sentrihome/Home-Security/ESPFirmwareV2/3d-Print/UART + Display layout_UART + Display layout v8_ESPsocketMount v8_2_Clamp2.stl

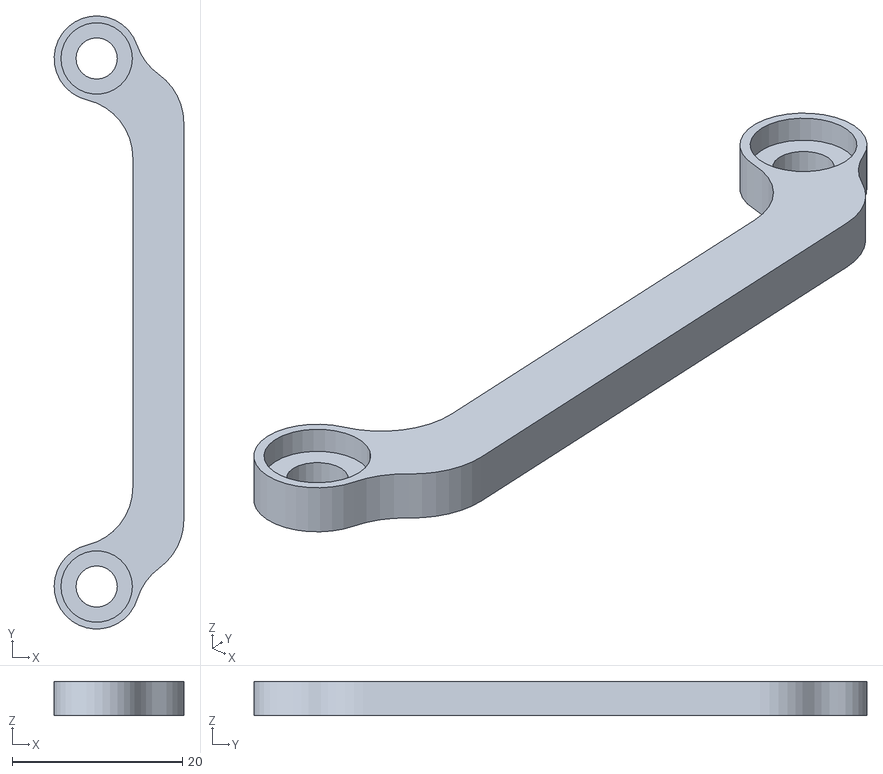
[picture p25: CAD file, 2026-08-16]
ESPFirmwareV2/3d-Print/UART + Display layout_UART + Display layout v8_ESPsocketMount v8_2_Clamp2.stl
15.3 x 72.1 x 4.00
