sentrihome/Home-Security/ESPFirmwareV2/Circuit/Circuit Drawings/HomeSecurity-Circuits-NPTH-drl_map.dxf

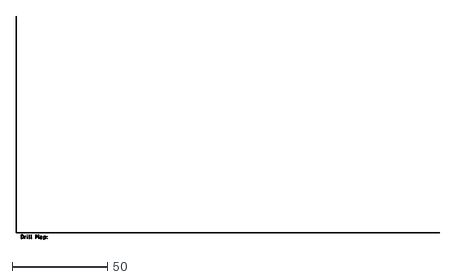
[picture p26: CAD file, 2026-08-16]
ESPFirmwareV2/Circuit/Circuit Drawings/HomeSecurity-Circuits-NPTH-drl_map.dxf
222.0 x 117.2
