sentrihome/Home-Security/ESPFirmwareV2/Circuit/Circuit Drawings/(Unsaved)_(Unsaved)_Body1.stl

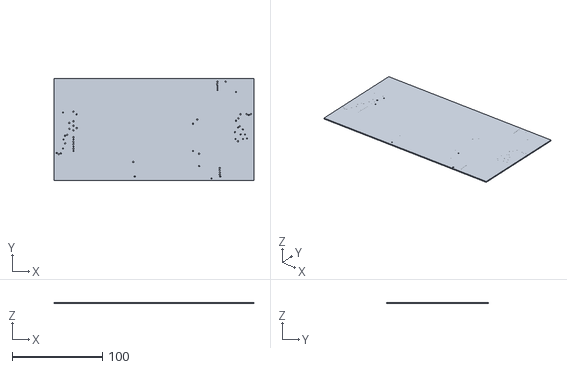
[picture p27: CAD file, 2026-08-16]
ESPFirmwareV2/Circuit/Circuit Drawings/(Unsaved)_(Unsaved)_Body1.stl
222.0 x 113.3 x 1.10
