sentrihome/Home-Security/ESPFirmwareV2/Circuit/Circuit Drawings/HomeSecurity-Circuits-B_Cu.dxf

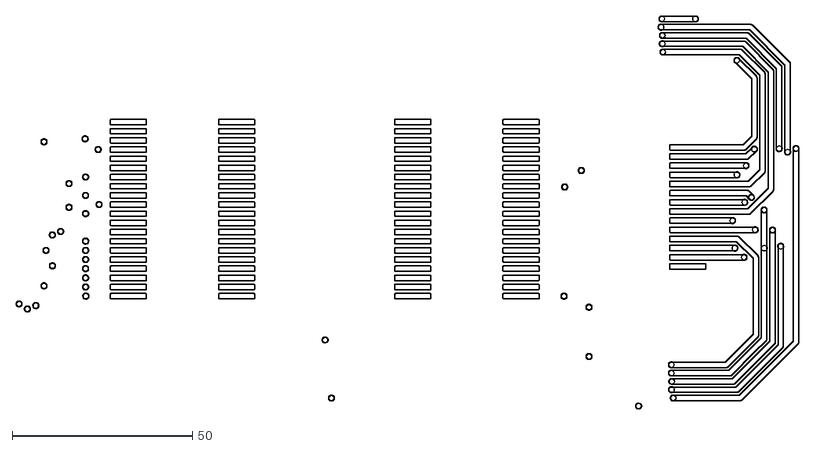
[picture p28: CAD file, 2026-08-16]
ESPFirmwareV2/Circuit/Circuit Drawings/HomeSecurity-Circuits-B_Cu.dxf
216.9 x 108.9
