sentrihome/Home-Security/ESPFirmwareV2/3d-Print/UART + Display layout_UART + Display layout v8_Body12.stl

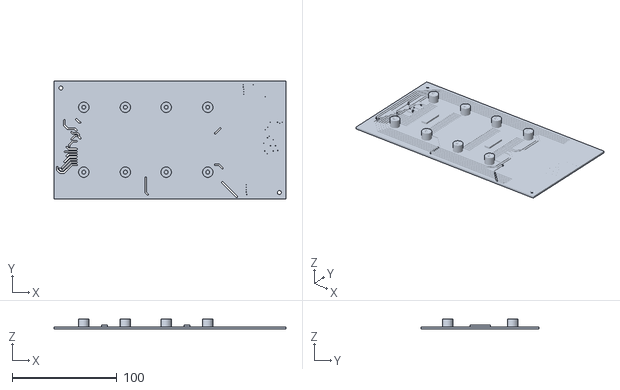
[picture p29: CAD file, 2026-08-16]
ESPFirmwareV2/3d-Print/UART + Display layout_UART + Display layout v8_Body12.stl
222.0 x 113.3 x 10.0
