sentrihome/Home-Security/ESPFirmwareV2/printed circuit/Untitled/Untitled.kicad_sch

## KiCad design ESPFirmwareV2/printed circuit/Untitled/Untitled.kicad_sch (2026-08-03)

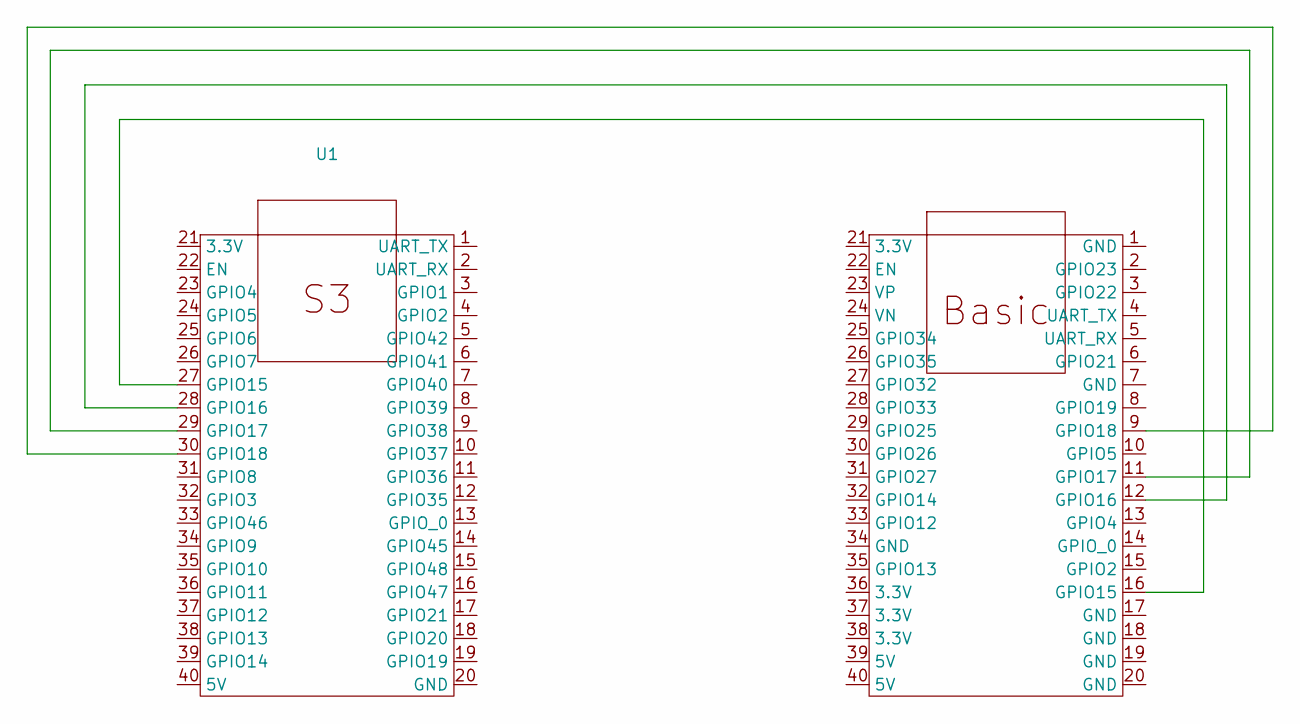
[picture p57: schematic Untitled.kicad_sch]

Parts:
U1, U2: esp32wroom

Connections:
unnamed: U1.27 (GPIO15), U2.16 (GPIO15)
unnamed: U1.28 (GPIO16), U2.12 (GPIO16)
unnamed: U1.29 (GPIO17), U2.11 (GPIO17)
unnamed: U1.30 (GPIO18), U2.9 (GPIO18)
