sentrihome/Home-Security/ESPFirmwareV2/centralconsole_ap/main/httpendpoints.cpp

#include "httpendpoints.h"
#include "connectivity.h"
#include <cstring>
#include <esp_wifi.h>
#include <esp_random.h>

QueueHandle_t waitfors3;

esp_err_t api_health_resp(httpd_req_t *r)
{
    return httpd_resp_sendstr(r, "{ \"health\": \"ok\" }");
}

esp_err_t api_pair_resp(httpd_req_t *r)
{
    char buf[1000];
    int length = httpd_req_recv(r, buf, sizeof(buf) - 1);
    if (length <= 0)
    {
        if (length == HTTPD_SOCK_ERR_TIMEOUT)
        {
            httpd_resp_send_408(r);
        }
        return ESP_FAIL;
    }
    buf[length] = '\0';

    std::string home_ssid = jsonparser(buf, "homessid");
    printf("Home SSID: %s\n", home_ssid.c_str());

    std::string home_pass = jsonparser(buf, "homepass");
    printf("Home Pass: %s\n", home_pass.c_str());

    std::string permanent_pass = jsonparser(buf, "permpass");
    printf("Permanent Pass: %s\n", permanent_pass.c_str());

    std::string encrypted_pass = jsonparser(buf, "encryptedpass");
    printf("Encrypted Pass: %s\n", encrypted_pass.c_str());

    std::string schedule_start = jsonparser(buf, "schedulestart");
    printf("Schedule Start: %s\n", schedule_start.c_str());

    std::string schedule_stop = jsonparser(buf, "schedulestop");
    printf("Schedule Stop: %s\n", schedule_stop.c_str());

    std::string raspberrypi_ip = jsonparser(buf, "raspberrypiip");
    printf("RaspberryPi IP: %s\n", raspberrypi_ip.c_str());

    uart.send(buf, cmd_s::MOBILE_PAIRING);
    printf("Relayed the data through UART");

    printf("Awaiting S3 Confirmation\n");

    std::string response_full;
    std::string *response_full_ptr = nullptr;
    if (xQueueReceive(waitfors3, &response_full_ptr, pdMS_TO_TICKS(6000)))
    {
        response_full = *response_full_ptr;
        delete response_full_ptr;
    }
    else
    {
        return httpd_resp_send_408(r);
    }
    std::string response_parsed_for_payload = jsonparser(response_full.c_str(), "pairing payload");
    std::string response_parsed_for_connection = jsonparser(response_full.c_str(), "wifiConnection");
    if ((response_parsed_for_payload == "received") && (response_parsed_for_connection == "true"))
    {
        printf("Received Confirmation from S3\n");

        char ap_password[33];
        for (int i = 0; i < 32; i++)
        {
            ap_password[i] = "ABCDEFGHIJKLMNOPQRSTUVWXYZabcdefghijklmnopqrstuvwxyz0123456789"[esp_random() % 62];
        }
        ap_password[32] = '\0';
        printf("New AP Password: %s\n", ap_password);

        //uart.send(ap_password, cmd_s::MOBILE_PAIRING);
        printf("Sent new AP password to sensor via UART\n");

        // ap_start("espwifi", ap_password);

        char resp_buf[256];
        snprintf(resp_buf, sizeof(resp_buf),
                 "{\"pairing payload\" : \"received\", \"wifiConnection\" : \"true\", \"new_ap_password\" : \"%s\"}",
                 ap_password);
        printf("http resp: {\"pairing payload\" : \"received\", \"wifiConnection\" : \"true\", \"new_ap_password\" : \"newpass\"}\n");
        return httpd_resp_sendstr(r, resp_buf);
    }
    else if ((response_parsed_for_payload == "received") && (response_parsed_for_connection == "false"))
    {
        printf("Received Confirmation from S3\n");
        printf("http resp {\"pairing payload\" : \"received\", \"wifiConnection\" : \"false\"}\n");
        return httpd_resp_sendstr(r, "{\"pairing payload\" : \"received\", \"wifiConnection\" : \"false\"}");
    }
    else if ((response_parsed_for_payload == "NO ACCESS"))
    {
        printf("No access from S3\n");
        printf("http resp { \"pairing payload received\": \"NO ACCESS\" }\n");
        return httpd_resp_sendstr(r, "{ \"pairing payload received\": \"NO ACCESS\" }");
    }
    else
    {
        printf("Received bad data from S3\n");
        printf("http resp { \"pairing payload received\": \"corrupted\" }\n");
        return httpd_resp_sendstr(r, "{ \"pairing payload received\": \"corrupted\" }");
    }

    // return httpd_resp_sendstr(r, "{ \"pairing payload received\": \"ok\" }");
}

esp_err_t api_motion_resp(httpd_req_t *r)
{
    char buf[200];
    int length = httpd_req_recv(r, buf, sizeof(buf) - 1);
    if (length <= 0)
    {
        if (length == HTTPD_SOCK_ERR_TIMEOUT)
        {
            httpd_resp_send_408(r);
        }
        return ESP_FAIL;
    }
    buf[length] = '\0';

    printf("From Motion: %s", buf);
    uart.send(buf, cmd_s::SENSOR);

    return httpd_resp_sendstr(r, "{ \"motion payload received\": \"ok\" }");
}

void endpoint_init()
{
    waitfors3 = xQueueCreate(1, sizeof(std::string *));
    // httpd_start(httpd_handle_t *handle, const httpd_config_t *config);
    httpd_handle_t api;
    httpd_config_t api_config = HTTPD_DEFAULT_CONFIG();
    api_config.stack_size = 8192;
    httpd_start(&api, &api_config);

    // httpd_register_uri_handler(httpd_handle_t handle, const httpd_uri_t *uri_handler);
    httpd_uri_t api_health_addr = {};
    api_health_addr.uri = "/health";
    api_health_addr.method = HTTP_GET;
    api_health_addr.handler = api_health_resp;
    httpd_register_uri_handler(api, &api_health_addr);

    httpd_uri_t api_pair_addr = {};
    api_pair_addr.uri = "/pair";
    api_pair_addr.method = HTTP_POST;
    api_pair_addr.handler = api_pair_resp;
    httpd_register_uri_handler(api, &api_pair_addr);

    httpd_uri_t api_motion_addr = {};
    api_motion_addr.uri = "/motion";
    api_motion_addr.method = HTTP_POST;
    api_motion_addr.handler = api_motion_resp;
    httpd_register_uri_handler(api, &api_motion_addr);
}
