sentrihome/Home-Security/ESPFirmwareV2/centralconsole_Station/main/jsonhandler.cpp

#include "jsonhandler.h"
#include "cJSON.h"

std::string jsonparser(const char *json_str, const char *key)
{
    if (json_str == nullptr || *json_str == '\0')
        return "__JSON_ERROR__";
    cJSON *root = cJSON_Parse(json_str);
    if (root == NULL)
        return "__JSON_ERROR__";

    cJSON *item = cJSON_GetObjectItem(root, key);
    if (cJSON_IsString(item))
    {
        // printf("%s\n", item->valuestring);
        std::string result = item->valuestring;
        cJSON_Delete(root);
        return result;
    }

    cJSON_Delete(root);
    return "";
}
