sentrihome/Home-Security/ESPFirmwareV2/centralconsole_Station/main/uielements.h

#pragma once
#include <stdint.h>

extern const uint8_t uiidle[];

extern const uint8_t uisysarmed[];
extern const uint8_t uisysarmed2[];
extern const uint8_t uisysarmed3[];

extern const uint8_t uisysdisarmed[];
extern const uint8_t uisysdisarmed2[];
extern const uint8_t uisysdisarmed3[];

extern const uint8_t uisettingspage_map[];
extern const uint8_t uihomepageUNarmed_map[];
extern const uint8_t uisetupinstructions_map[];
