sentrihome/Home-Security/ESP32_Files/vscodeESPIDF/s3-Display-firmware4.4.6/main/wificonfig.cpp

#include "wificonfig.h"


const char* DEVICE_NAME = "ESP_DISPLAY";
const char* targetIP = "192.168.10.2"; 
const int udpPort = 5005;
WiFiUDP udp;
unsigned long lastSend = 0;
char wifiReceiveBuffer[128];
String wifissid;
String wifipassword;

void wifi_send(const char* message) {
  if (millis() - lastSend > 1000) {
    lastSend = millis();

    for (int i = 0; i < idscount; i++) {
      if (IDS[i].length() > 0) {
        udp.beginPacket(IDS[i].c_str(), udpPort);
        udp.print(message);
        udp.endPacket();
      }
    }
    

    Serial.println("Sent message");
  }
}

void wifi_receive(void) {
  static char buf[128];   // static avoids stack churn (nice on ESP32)

  int packetSize = udp.parsePacket();
  if (packetSize <= 0) return;

  int len = udp.read(buf, sizeof(buf) - 1);
  if (len <= 0) return;

  buf[len] = '\0';

  Serial.print("Received: ");
  Serial.println(buf);

  // Robust command match (ignores trailing junk)
  if (strncmp(buf, "INTRUDER INTRUDER", 16) == 0) {

    udp.beginPacket("192.168.0.202", 5005);
    udp.print("INTRUDER INTRUDER\n");
    udp.endPacket();
    myServo.write(0);    // 0°
    delay(350);
    myServo.write(180);   // 90°
    delay(350);
    myServo.write(0);  // 180°
    delay(350);
  }

}

bool wifiapstart(){
  IPAddress apIP(192,168,10,1);
  IPAddress gateway(192,168,10,1);
  IPAddress subnet(255,255,255,0);
  WiFi.softAPConfig(apIP, gateway, subnet);

  const int maxTries = 3;
  for (int i = 0; i < maxTries; i++) {
    if (WiFi.softAP("ESP32_Master_Config","", 11)) {
      // Wait until AP actually has an IP (ready to serve)
      unsigned long start = millis();
      while (WiFi.softAPIP()[0] == 0 && (millis() - start < 5000)) {
        delay(50);
      }
      if (WiFi.softAPIP()[0] != 0) {
        Serial.printf("AP started, IP: %s\n", WiFi.softAPIP().toString().c_str());
        return true;
      }
    }
    Serial.printf("AP start attempt %d failed, retrying...\n", i + 1);
    delay(1000);
  }
  Serial.println("AP failed to start after retries");
  return false;
}

String memoryssid = "";
String memorypass = "";
void getcred(){
  memoryssid = littlefsReadFile("/wifissid.txt");
  memorypass = littlefsReadFile("/wifipass.txt");
}

void wifistastart(){
  getcred();
  WiFi.begin(memoryssid, memorypass);
  Serial.printf("WifiConnected");
}

static bool serverStarted = false;
void wifiInit(){
  WiFi.mode(WIFI_AP_STA);
  wifiapstart();
  if (!wifiapstart()) {
    Serial.println("Warning: AP did not start; continuing with STA only.");
  }
  delay(1000);
  wifistastart();
  udp.begin(udpPort);
}

void setuppageserver(){
  if (!homepage && setuppage && !disarmauthpage){
        
    if (!serverStarted) {
        server.begin();
        serverStarted = true;
        Serial.print("server started");
    }
    server.handleClient();
  }
  else{
      if (serverStarted) {
        server.stop();
        serverStarted = false;
        Serial.print("server stopped");
      }
  }
}
